Lacybad/Weather-Station/weatherPCB/Simulations/BJT_HighSideSwitch.asc

Q1: npn; 2N4401
Q2: pnp; 2N4403
R1: res; 4.7k
R2: res; 4.7k
R3: res; 1.7k
V1: voltage; PULSE(0 3.3 0 0 0 .01 .02)
V2: voltage; 3.3
Named nets: 0
.tran 0 .10 0 .001
Load
