Lacybad/Weather-Station/Settings.h

#define _MISCSETTINGS_H
#ifdef _MISCSETTINGS_H
#include "MiscSettings.h" //use personal settings
#else

//if file is not defined
#ifndef STASSID
#define STASSID "SSID"
#define STAPSK  "PSWD"
#endif
//OpenWeatherMap api key (example)
#define API_KEY "abcdef0123456789"
//example, is NYC
#define LAT "40.7828687"
#define LON "-73.9675438"
#define FORECAST_LOC "lat=" LAT "&lon=" LON
#endif

//Other vars
#define UPDATE_INTERVAL 2*60UL
#define UPDATE_INTERVAL_MOTION 20UL //optional, stops rapid update with no motion
#define PIR_TIME 30UL    //time to keep display on, in seconds
//#define PIR_TIME 1UL * 60UL //for minutes, can change 1UL to xxUL
#define PIR_ON_TIME 5
#define PIR_OFF_TIME 12+11
//#define PIR_OFF_TIME_MORNING 1    //uncomment if off time is 12am or later

//humidity or not
#define PRECIP_INSTY //use precip intensity, else use humidity
//units
#define UNITS "imperial" //units using
#define PRECIP_UNIT "in" //to print out
