Lacybad/Weather-Station/src/cert.h

//Cert from https://api.darksky.net
//Get root cert, download to cert.crt, run bash script convertCert.sh
#define USE_CERT
static const char digicert[] PROGMEM = R"EOF(
-----BEGIN CERTIFICATE-----
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
rqXRfboQnoZsG4q5WTP468SQvvG5
-----END CERTIFICATE-----
)EOF";
